shaise/OpenSkySim/Software/Src/debug.c

/*
    Copyright 2017 fishpepper <AT> gmail.com

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
   author: fishpepper <AT> gmail.com
*/

#include "debug.h"
#include "timeout.h"

#if DEBUG
extern UART_HandleTypeDef huart1;


debug_buffer_t debug_buffer;
uint8_t debug_init_done = 0;

#ifdef UART_DEBUG
static volatile uint8_t send_in_progress = 0;

void debug_int_enable()
{
  __HAL_UART_ENABLE_IT(&huart1, UART_IT_TXE);
}

void debug_int_disable()
{
  __HAL_UART_DISABLE_IT(&huart1, UART_IT_TXE);
}
#endif


void debug_init(void) {
#ifdef UART_DEBUG
    debug_uart_init();
#endif
    debug_init_done = 1;

    //debug_put_newline();
    debug("### OpenSky - sim");
    debug(" - (c) by github.com/shaise ###\n"); debug_flush();
    debug("uart: init done\n");
}

void debug_start_transmission(uint8_t ch)
{
#ifdef UART_DEBUG
  huart1.Instance->DR = ch;
  send_in_progress = 1;

#else
	ITM_SendChar(ch);
#endif
}

#ifdef UART_DEBUG

void debug_uart_init(void) {
    debug_buffer.write = 0;
    debug_buffer.read = 0;

    // wait some time for uart to become stable
    delay_us(100);
}

// called from stm32f1xx_it.c
void debug_isr(void) {
  //HAL_DEBUG_ISR_CLEAR_FLAG();
  if (!send_in_progress)
    return;
  // finished with sending?
  if (debug_buffer.read == debug_buffer.write) {
    // no data in fifo -> disable tx int:
    debug_int_disable();
    send_in_progress = 0;
    return;
  }

  // else: data to tx
  huart1.Instance->DR = debug_buffer.data[debug_buffer.read];

  // handle out pointer
  debug_buffer.read = (debug_buffer.read + 1) & DEBUG_TX_BUFFER_AND_OPERAND;

}

void debug_uart_test(void) {
    debug("uart: running test\n"); debug_flush();
    while (1) {
        debug("TEST12345\n");
        delay_ms(500);
    }
}
#endif

void debug_putc(uint8_t ch) {
    // add \r to newlines
    if (ch == '\n') debug_putc('\r');

#ifdef UART_DEBUG
    // disable interrupts
    debug_int_disable();

    if (send_in_progress) {
        // int already active, copy to buffer!
        debug_buffer.data[debug_buffer.write] = ch;
        debug_buffer.write = (debug_buffer.write + 1) & DEBUG_TX_BUFFER_AND_OPERAND;

        // check if free space in buffer:
        if (debug_buffer.write == debug_buffer.read) {
            // no more space in buffer! this will loose some data!
            // add LOST data tag (for visual debugging lost data)
            debug_buffer.write = (debug_buffer.write - 1) & DEBUG_TX_BUFFER_AND_OPERAND;
            debug_buffer.data[debug_buffer.write] = '$';

            /*LED_RED_ON();
            LED_GREEN_OFF();
            while (1) {
                LED_RED_ON();
                LED_GREEN_ON();
                delay_ms(200);
                LED_RED_OFF();
                LED_GREEN_OFF();
                delay_ms(200);
            }*/
        }
    } else {
        // no int active. send first byte and reset buffer indices
        debug_buffer.write  = debug_buffer.read;

        debug_start_transmission(ch);
    }

    // re enable interrupts
    debug_int_enable();
#else
    debug_start_transmission(ch);
#endif
}

void debug_flush(void) {
    if (!debug_init_done) {
        return;
    }
    // wait until uart buffer is empty
    // once TX INT is disabled our buffer is empty again
#ifdef UART_DEBUG
    while (send_in_progress) {}
#endif
}


void debug(char *data) {
    char c = *data++;
    while (c) {
        debug_putc((uint8_t)c);
        c = *data++;
    }
}


// put hexadecimal number to debug out.
void debug_put_hex8(uint8_t val) {
    uint8_t lo = val&0x0F;
    uint8_t hi = val >> 4;
    if (hi < 0x0A) {
        hi = '0' + hi;
    } else {
        hi = 'A' - 0x0A + hi;
    }

    if (lo < 0x0A) {
        lo = '0' + lo;
    } else {
        lo = 'A' - 0x0A + lo;
    }
    debug_putc(hi);
    debug_putc(lo);
}

// put 16bit hexadecimal number to debug out
void debug_put_hex16(uint16_t val) {
    debug_put_hex8(val>>8);
    debug_put_hex8(val & 0xFF);
}

// put 32bit hexadecimal number to debug out
void debug_put_hex32(uint32_t val) {
    debug_put_hex8(val>>24);
    debug_put_hex8(val>>16);
    debug_put_hex8(val>> 8);
    debug_put_hex8(val & 0xFF);
}

// output a signed 8-bit number to uart
void debug_put_int8(int8_t c) {
    uint8_t tmp;
    uint8_t mul;
    uint8_t l;
    uint8_t uint_s;

    if (c < 0) {
        debug_putc('-');
        uint_s = -c;
    } else {
        uint_s = c;
    }

    l = 0;
    for (mul = 100; mul > 0; mul = mul / 10) {
        tmp = '0';
        while (uint_s >= mul) {
            uint_s -= mul;
            tmp++;
            l = 1;
        }
        if ((l == 0) && (tmp == '0') && (mul != 1)) {
            // dont print spacer
            // debug_putc(' ');
        } else {
            debug_putc(tmp);
        }
    }
}

// output an unsigned 8-bit number to uart
void debug_put_uint8(uint8_t c) {
    uint8_t tmp;
    uint8_t mul;
    uint8_t l;

    l = 0;
    for (mul = 100; mul > 0; mul = mul / 10) {
        tmp = '0';
        while (c >= mul) {
            c -= mul;
            tmp++;
            l = 1;
        }
        if ((l == 0) && (tmp == '0') && (mul != 1)) {
            // dont print spacer
            // debug_putc(' ');
        } else {
            debug_putc(tmp);
        }
    }
}

// output an unsigned 16-bit number to uart
// FIXME: this routine is somewhat buggy when used with the ISR fifo debug_putc
//       it is still unclear why this is causing problems?!
void debug_put_uint16(uint16_t c) {
    uint8_t tmp;
    uint8_t l = 0;
    // loop unrolling is better (no int16 arithmetic)
    /*for (mul=10000; mul>0; mul = mul/10) {
        uint16_t mul;

        l=0;
                tmp = '0';
                while (c>=mul) {
                        c -= mul;
                        tmp++;
                        l=1;
                }
                if ((l==0) && (tmp == '0') && (mul!=1)) {
                        // debug_putc(' ');
                } else {
                        debug_putc(tmp);
                }
        }*/
    tmp = 0;
    while (c >= 10000L) {
        c -= 10000L;
        tmp++;
        l = 1;
    }
    if (tmp != 0) debug_putc('0' + tmp);

    tmp = 0;
    while (c >= 1000L) {
        c -= 1000L;
        tmp++;
        l = 1;
    }
    if (l || (tmp != 0)) debug_putc('0' + tmp);

    tmp = 0;
    while (c >= 100) {
        c -= 100;
        tmp++;
        l = 1;
    }
    if (l || (tmp != 0)) debug_putc('0' + tmp);

    tmp = 0;
    while (c >= 10) {
        c -= 10;
        tmp++;
        l = 1;
    }
    if (l || (tmp != 0)) debug_putc('0' + tmp);

    debug_putc('0' + (uint8_t)c);
}

void debug_put_newline(void) {
    debug_putc('\n');
}

#endif  // DEBUG
