shaise/OpenSkySim/Software/Inc/timeout.h

/*
 * timeout.h
 *
 *  Created on: Nov 14, 2020
 *      Author: shai
 */

#ifndef TIMEOUT_H_
#define TIMEOUT_H_

#include "stm32f1xx_it.h"
#define delay_ms(ms) timeout_delay_ms(ms)

#endif /* TIMEOUT_H_ */
